Bylin-code/Yappl/src/drivers/piezo_buzzer.cpp

#include "drivers/piezo_buzzer.h"

#include "app/config.h"

namespace yappl {

bool PiezoBuzzer::begin() {
  pinMode(AppConfig::piezoPin, OUTPUT);
  // Ensure the piezo is quiet after boot and after reflashing.
  stop();
  started_ = true;
  return true;
}

void PiezoBuzzer::play(uint16_t frequencyHz) {
  if (!started_ || frequencyHz == 0) {
    return;
  }

  // tone() owns the timer output until noTone() is called or the frequency is
  // changed by another tone() call.
  tone(AppConfig::piezoPin, frequencyHz);
}

void PiezoBuzzer::playFor(uint16_t frequencyHz, uint32_t durationMs) {
  if (!started_ || frequencyHz == 0 || durationMs == 0) {
    return;
  }

  // This returns immediately; Arduino's tone timer handles the duration.
  tone(AppConfig::piezoPin, frequencyHz, durationMs);
}

void PiezoBuzzer::stop() {
  // noTone releases Arduino's tone timer for this pin.
  noTone(AppConfig::piezoPin);
  // Drive low afterward so the passive piezo is less likely to float/buzz.
  digitalWrite(AppConfig::piezoPin, LOW);
}

}  // namespace yappl
